smartboxchannel/EFEKTA-Open_PM_Monitor/IMAGES/001.jpg

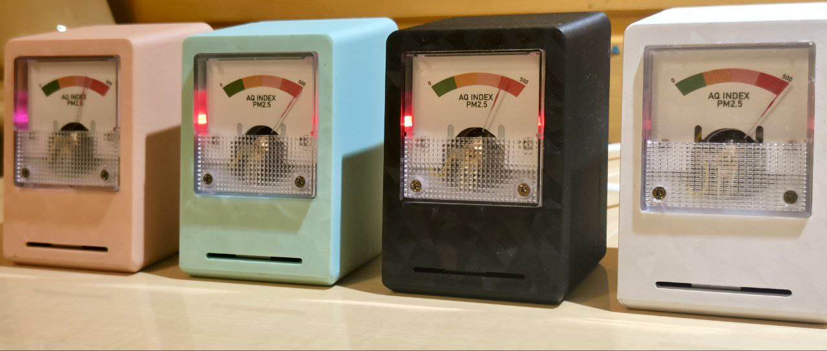
IMAGES/001.jpg
