smartboxchannel/EFEKTA-Open_PM_Monitor/IMAGES/002.jpg

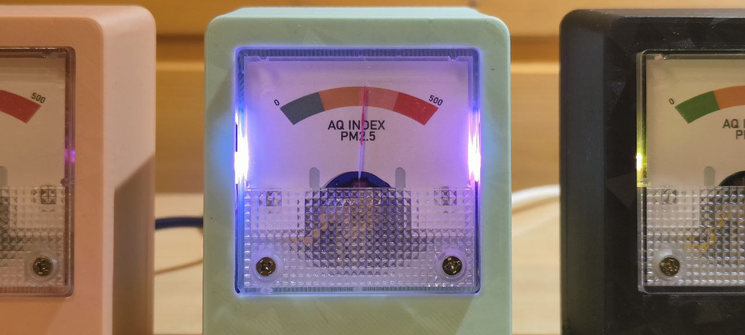
IMAGES/002.jpg
