smartboxchannel/EFEKTA-Open_PM_Monitor/IMAGES/image (5).png

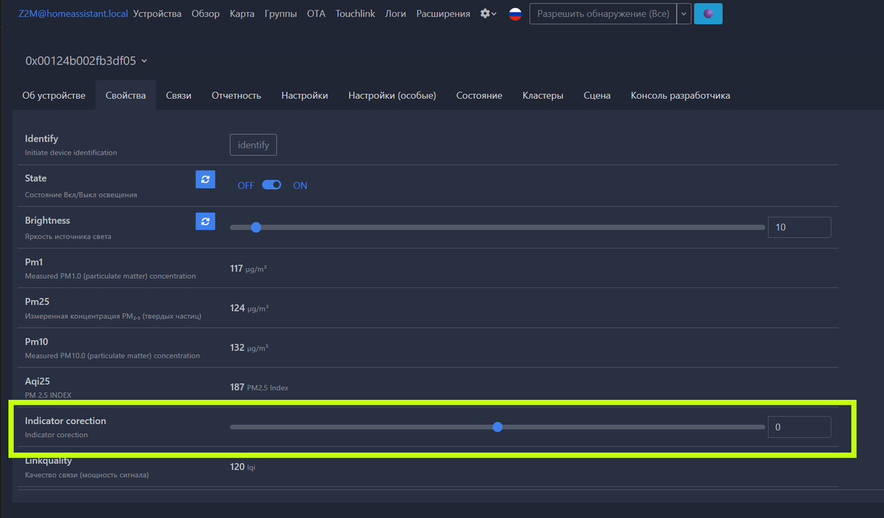
IMAGES/image (5).png
