smartboxchannel/EFEKTA-Open_PM_Monitor/PROJECT SOURCE/zstack-lib/hal_i2c.c

/**************************************************************************************************
  Filename:       hal_i2c.c
  Revised:        $Date: 2012-09-21 06:30:38 -0700 (Fri, 21 Sep 2012) $
  Revision:       $Revision: 31581 $

  Description:    This module defines the HAL I2C API for the CC2541ST. It
                  implements the I2C master.

  Copyright 2012 Texas Instruments Incorporated. All rights reserved.

  IMPORTANT: Your use of this Software is limited to those specific rights
  granted under the terms of a software license agreement between the user
  who downloaded the software, his/her employer (which must be your employer)
  and Texas Instruments Incorporated (the "License").  You may not use this
  Software unless you agree to abide by the terms of the License. The License
  limits your use, and you acknowledge, that the Software may not be modified,
  copied or distributed unless embedded on a Texas Instruments microcontroller
  or used solely and exclusively in conjunction with a Texas Instruments radio
  frequency transceiver, which is integrated into your product.  Other than for
  the foregoing purpose, you may not use, reproduce, copy, prepare derivative
  works of, modify, distribute, perform, display or sell this Software and/or
  its documentation for any purpose.

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
  Should you have any questions regarding your right to use this Software,
  contact Texas Instruments Incorporated at www.TI.com.
**************************************************************************************************/

/*********************************************************************
 * INCLUDES
 *********************************************************************/

#include "hal_i2c.h"

#include "ioCC2530.h"
#include "zcomdef.h"
#include "utils.h"

/*********************************************************************
 * MACROS
 *********************************************************************/

#define STATIC static

#if !defined HAL_I2C_RETRY_CNT
#define HAL_I2C_RETRY_CNT 3
#endif

// Default configuration uses P0.6 for SDA and P0.5 for SCL.
// Change these as needed.
#ifndef OCM_CLK_PORT
#define OCM_CLK_PORT 0
#endif

#ifndef OCM_DATA_PORT
#define OCM_DATA_PORT 0
#endif

#ifndef OCM_CLK_PIN
#define OCM_CLK_PIN 5
#endif

#ifndef OCM_DATA_PIN
#define OCM_DATA_PIN 6
#endif

#define OCM_ADDRESS (0xA0)

#define SMB_ACK         (0)
#define SMB_NAK         (1)
#define SEND_STOP       (0)
#define NOSEND_STOP     (1)
#define SEND_START      (0)
#define NOSEND_START    (1)

// OCM port I/O definitions
#define OCM_SCL BNAME(OCM_CLK_PORT, OCM_CLK_PIN)
#define OCM_SDA BNAME(OCM_DATA_PORT, OCM_DATA_PIN)

#define OCM_DATA_HIGH() { IO_DIR_PORT_PIN(OCM_DATA_PORT, OCM_DATA_PIN, IO_IN); }

#define OCM_DATA_LOW()                                                                                                                     \
    {                                                                                                                                      \
        IO_DIR_PORT_PIN(OCM_DATA_PORT, OCM_DATA_PIN, IO_OUT);                                                                              \
        OCM_SDA = 0;                                                                                                                       \
    }

/*********************************************************************
 * LOCAL VARIABLES
 *********************************************************************/

STATIC uint8 s_xmemIsInit;

/*********************************************************************
 * LOCAL FUNCTIONS PROTOTYPES
 *********************************************************************/

STATIC void hali2cSend(uint8 *buffer, uint16 len, uint8 sendStart, uint8 sendStop);
STATIC _Bool hali2cSendByte(uint8 dByte);
STATIC _Bool hali2cSendByte2(uint8 dByte);
STATIC void hali2cWrite(bool dBit);
STATIC void hali2cWrite2(bool dBit);
STATIC void hali2cClock(bool dir);
STATIC void hali2cClock2(bool dir);
STATIC void hali2cStart(void);
STATIC void hali2cStop(void);
STATIC void hali2cReceive(uint8 address, uint8 *buffer, uint16 len);
STATIC uint8 hali2cReceiveByte(void);
STATIC _Bool hali2cRead(void);
STATIC void hali2cSendDeviceAddress(uint8 address);
STATIC __near_func void hali2cWait(uint8);
static void hali2cGroudPins(void);

/*********************************************************************
 * @fn      hali2cGroudPins
 * @brief   Set I2C pins to input mode
 *********************************************************************/

static void hali2cGroudPins(void)
{
    IO_DIR_PORT_PIN(OCM_DATA_PORT, OCM_DATA_PIN, IO_IN);
    IO_DIR_PORT_PIN(OCM_CLK_PORT, OCM_CLK_PIN, IO_IN);
}

/*********************************************************************
 * @fn      HalI2CInit
 * @brief   Initializes two-wire serial I/O bus
 *********************************************************************/

void HalI2CInit(void)
{
    if (!s_xmemIsInit) {
        s_xmemIsInit = 1;

        // // Set port pins as inputs
        // IO_DIR_PORT_PIN(OCM_CLK_PORT, OCM_CLK_PIN, IO_IN);
        // IO_DIR_PORT_PIN(OCM_DATA_PORT, OCM_DATA_PIN, IO_IN);
        // //
        // // Set for general I/O operation
        // IO_FUNC_PORT_PIN(OCM_CLK_PORT, OCM_CLK_PIN, IO_GIO);
        // IO_FUNC_PORT_PIN(OCM_DATA_PORT, OCM_DATA_PIN, IO_GIO);
        // //
        // // Set I/O mode for pull-up/pull-down
        // IO_IMODE_PORT_PIN(OCM_CLK_PORT, OCM_CLK_PIN, IO_PUD);
        // IO_IMODE_PORT_PIN(OCM_DATA_PORT, OCM_DATA_PIN, IO_PUD);

        // // Set pins to pull-up
        // IO_PUD_PORT(OCM_CLK_PORT, IO_PUP);
        // IO_PUD_PORT(OCM_DATA_PORT, IO_PUP);
    }
}

/*********************************************************************
 * @fn      HalI2CReceive
 * @brief   Receives data into a buffer from an I2C slave device
 *********************************************************************/

int8 HalI2CReceive(uint8 address, uint8 *buf, uint16 len)
{
    hali2cReceive(address, buf, len);
    return 0;
}

/*********************************************************************
 * @fn      HalI2CSend
 * @brief   Sends buffer contents to an I2C slave device
 *********************************************************************/

int8 HalI2CSend(uint8 address, uint8 *buf, uint16 len)
{
    // Begin the write sequence with the address byte
    hali2cSendDeviceAddress(address);
    hali2cSend(buf, len, NOSEND_START, SEND_STOP);
    return 0;
}

/*********************************************************************
 * @fn      hali2cSend
 * @brief   Sends buffer contents to SM-Bus device
 *********************************************************************/

STATIC void hali2cSend(uint8 *buffer, uint16 len, uint8 sendStart, uint8 sendStop)
{
    uint16 i;
    uint8 retry = HAL_I2C_RETRY_CNT;

    if (!len) {
        return;
    }

    if (sendStart == SEND_START) {
        hali2cStart();
    }

    for (i = 0; i < len; i++) {
        do {
            if (hali2cSendByte(buffer[i])) // Takes care of ack polling
            {
                break;
            }
        } while (--retry);
    }

    if (sendStop == SEND_STOP) {
        hali2cStop();
    }
}

/*********************************************************************
 * @fn      hali2cSendByte
 * @brief   Serialize and send one byte to SM-Bus device
 * @return  ACK status - 0=none, 1=received
 *********************************************************************/

STATIC _Bool hali2cSendByte(uint8 dByte)
{
    uint8 i;

    for (i = 0; i < 8; i++) {
        // Send the MSB
        hali2cWrite(dByte & 0x80);
        // Next bit into MSB
        dByte <<= 1;
    }
    // Need clock low so if the SDA transitions on the next statement the
    // slave doesn't stop. Also give opportunity for slave to set SDA
    hali2cClock(0);
    OCM_DATA_HIGH(); // Set to input to receive ack...
    hali2cClock(1);
    hali2cWait(1);

    return (!OCM_SDA); // Return ACK status
}

/*********************************************************************
 * @fn      hali2cWrite
 * @brief   Send one bit to SM-Bus device
 *********************************************************************/

STATIC void hali2cWrite(bool dBit)
{
    hali2cClock(0);
    hali2cWait(1);
    if (dBit) {
        OCM_DATA_HIGH();
    } else {
        OCM_DATA_LOW();
    }

    hali2cClock(1);
    hali2cWait(1);
}

/*********************************************************************
 * @fn      hali2cClock
 * @brief   Clocks the SM-Bus. If a negative edge is going out, the
 *          I/O pin is set as an output and driven low. If a positive
 *          edge is going out, the pin is set as an input and the pin
 *          pull-up drives the line high. This way, the slave device
 *          can hold the node low if longer setup time is desired.
 *********************************************************************/

STATIC void hali2cClock(bool dir)
{
    uint8 maxWait = 10;
    if (dir) {
        IO_DIR_PORT_PIN(OCM_CLK_PORT, OCM_CLK_PIN, IO_IN);
        /* Wait until clock is high */
        while (!OCM_SCL && maxWait) {
            hali2cWait(1);
            maxWait -= 1;
        }
    } else {
        IO_DIR_PORT_PIN(OCM_CLK_PORT, OCM_CLK_PIN, IO_OUT);
        OCM_SCL = 0;
    }
    hali2cWait(1);
}

/*********************************************************************
 * @fn      hali2cClock2
 * @brief   Simplified clock function without delay
 *********************************************************************/

STATIC void hali2cClock2(bool dir)
{
    uint8 maxWait = 5;
    if (dir) {
        IO_DIR_PORT_PIN(OCM_CLK_PORT, OCM_CLK_PIN, IO_IN);
        /* Wait until clock is high */
        while (!OCM_SCL && maxWait) {
            maxWait -= 1;
        }
    } else {
        IO_DIR_PORT_PIN(OCM_CLK_PORT, OCM_CLK_PIN, IO_OUT);
        OCM_SCL = 0;
    }
}

/*********************************************************************
 * @fn      hali2cStart
 * @brief   Initiates SM-Bus communication. Makes sure that both the
 *          clock and data lines of the SM-Bus are high. Then the data
 *          line is set high and clock line is set low to start I/O.
 *********************************************************************/

STATIC void hali2cStart(void)
{
    uint8 retry = HAL_I2C_RETRY_CNT;

    // Set SCL to input but with pull-up. If slave is pulling down it will stay down.
    hali2cClock(1);

    do {
        // Wait for slave to release clock line...
        if (OCM_SCL) // Wait until the line is high...
        {
            break;
        }
        hali2cWait(1);
    } while (--retry);

    // SCL low to set SDA high so the transition will be correct.
    hali2cClock(0);
    OCM_DATA_HIGH(); // SDA high
    hali2cClock(1);  // Set up for transition
    hali2cWait(1);
    OCM_DATA_LOW(); // Start condition

    hali2cWait(1);
    hali2cClock(0);
}

/*********************************************************************
 * @fn      hali2cStop
 * @brief   Terminates SM-Bus communication. Waits until the data line
 *          is low and the clock line is high. Then sets the data line
 *          high, keeping the clock line high to stop I/O.
 *********************************************************************/

STATIC void hali2cStop(void)
{
    // Wait for clock high and data low
    hali2cClock(0);
    OCM_DATA_LOW(); // Force low with SCL low
    hali2cWait(1);

    hali2cClock(1);
    OCM_DATA_HIGH(); // Stop condition
    hali2cWait(1);

    hali2cGroudPins();
}

/*********************************************************************
 * @fn      hali2cWait
 * @brief   Busy-wait delay
 *********************************************************************/

STATIC __near_func void hali2cWait(uint8 count)
{
    while (count--) {
        asm("NOP");
    }
}

/*********************************************************************
 * @fn      hali2cReceiveByte
 * @brief   Read the 8 data bits
 *********************************************************************/

STATIC uint8 hali2cReceiveByte()
{
    int8 i, rval = 0;

    for (i = 7; i >= 0; --i) {
        if (hali2cRead()) {
            rval |= 1 << i;
        }
    }

    return rval;
}

/*********************************************************************
 * @fn      hali2cReceive
 * @brief   Reads data into a buffer
 *********************************************************************/

STATIC void hali2cReceive(uint8 address, uint8 *buffer, uint16 len)
{
    uint16 i;

    if (!len) {
        return;
    }

    hali2cSendDeviceAddress(address);

    for (i = 0; i < len - 1; i++) {
        // SCL may be high. Set SCL low. If SDA goes high when input
        // mode is set the slave won't see a STOP
        hali2cClock(0);
        OCM_DATA_HIGH();

        buffer[i] = hali2cReceiveByte();
        hali2cWrite(SMB_ACK); // Write leaves SCL high
    }

    // Condition SDA one more time...
    hali2cClock(0);
    OCM_DATA_HIGH();
    buffer[i] = hali2cReceiveByte();
    hali2cWrite(SMB_NAK);

    hali2cStop();
}

/*********************************************************************
 * @fn      hali2cRead
 * @brief   Toggle the clock line to let the slave set the data line.
 *          Then read the data line.
 * @return  TRUE if bit read is 1 else FALSE
 *********************************************************************/

STATIC _Bool hali2cRead(void)
{
    // SCL low to let slave set SDA. SCL high for SDA
    // valid and then get bit
    hali2cClock(0);
    hali2cWait(1);
    hali2cClock(1);
    hali2cWait(1);

    return OCM_SDA;
}

/*********************************************************************
 * @fn      hali2cSendDeviceAddress
 * @brief   Send only the device address with ACK polling
 *********************************************************************/

STATIC void hali2cSendDeviceAddress(uint8 address)
{
    uint8 retry = HAL_I2C_RETRY_CNT;

    do {
        hali2cStart();
        if (hali2cSendByte(address)) // Do ack polling...
        {
            break;
        }
    } while (--retry);
}

/*********************************************************************
 * @fn      I2C_ReadMultByte
 * @brief   Reads multiple bytes from an I2C device register
 *********************************************************************/

int8 I2C_ReadMultByte(uint8 address, uint8 reg, uint8 *buffer, uint16 len)
{
    uint16 i = 0;
    uint8 _address = 0;

    if (!len) {
        return I2C_ERROR;
    }

    /* Send START condition */
    hali2cStart();

    /* Set direction of transmission */
    _address = ((address << 1) | OCM_WRITE);

    /* Send Address and get acknowledgement from slave */
    if (!hali2cSendByte(_address)) {
        return I2C_ERROR;
    }

    /* Send internal register to read from */
    if (!hali2cSendByte(reg)) {
        return I2C_ERROR;
    }

    /* Send RESTART condition */
    hali2cStart();

    /* Set direction of transmission */
    _address = ((address << 1) | OCM_READ);
    /* Send Address and get acknowledgement from slave */
    if (!hali2cSendByte(_address)) {
        return I2C_ERROR;
    }

    while (len) {
        // SCL may be high. Set SCL low. If SDA goes high when input
        // mode is set the slave won't see a STOP
        hali2cClock(0);
        OCM_DATA_HIGH();
        buffer[i] = hali2cReceiveByte();
        // Acknowledgement if not sending last byte
        if (len > 1) {
            hali2cWrite(SMB_ACK); // Write leaves SCL high
        }

        // Increment buffer register
        i++;
        // Decrement the read bytes counter
        len--;
    }

    // Condition SDA one more time...
    hali2cClock(0);
    OCM_DATA_HIGH();
    hali2cWrite(SMB_NAK);

    hali2cStop();

    return I2C_SUCCESS;
}

/*********************************************************************
 * @fn      I2C_WriteMultByte
 * @brief   Writes multiple bytes to an I2C device register
 *********************************************************************/

int8 I2C_WriteMultByte(uint8 address, uint8 reg, uint8 *buffer, uint16 len)
{
    uint16 i = 0;
    uint8 _address = 0;

    if (!len) {
        return I2C_ERROR;
    }

    /* Send START condition */
    hali2cStart();

    /* Set direction of transmission */
    _address = ((address << 1) | OCM_WRITE);

    /* Send Address and get acknowledgement from slave */
    if (!hali2cSendByte(_address)) {
        return I2C_ERROR;
    }

    /* Send internal register to write to */
    if (!hali2cSendByte(reg)) {
        return I2C_ERROR;
    }

    /* Write data into register */
    while (len) {
        /* Send data byte and get acknowledgement from slave */
        if (!hali2cSendByte2(buffer[i])) {
            return I2C_ERROR;
        }

        // Increment buffer register
        i++;
        // Decrement the write bytes counter
        len--;
    }

    hali2cStop();
    return I2C_SUCCESS;
}

/*********************************************************************
 * @fn      hali2cSendByte2
 * @brief   Serialize and send one byte (optimized version)
 *********************************************************************/

STATIC _Bool hali2cSendByte2(uint8 dByte)
{
    uint8 i;

    for (i = 0; i < 8; i++) {
        // Send the MSB
        hali2cWrite2(dByte & 0x80);
        // Next bit into MSB
        dByte <<= 1;
    }
    // Need clock low so if the SDA transitions on the next statement the
    // slave doesn't stop. Also give opportunity for slave to set SDA
    hali2cClock2(0);
    OCM_DATA_HIGH(); // Set to input to receive ack...
    hali2cClock2(1);

    return (!OCM_SDA); // Return ACK status
}

/*********************************************************************
 * @fn      hali2cWrite2
 * @brief   Send one bit (optimized version)
 *********************************************************************/

STATIC void hali2cWrite2(bool dBit)
{
    hali2cClock2(0);
    if (dBit) {
        OCM_DATA_HIGH();
    } else {
        OCM_DATA_LOW();
    }
    hali2cClock2(1);
}
