smartboxchannel/EFEKTA-Open_PM_Monitor/PROJECT SOURCE/Source/zcl_ota.h

/******************************************************************************
 * Filename:       zcl_ota.h
 * Description:    ZCL Over-the-Air Upgrade Cluster definitions
 *
 * Copyright 2010-2014 Texas Instruments Incorporated. All rights reserved.
 *****************************************************************************/

#ifndef ZCL_OTA_H
#define ZCL_OTA_H

#ifdef __cplusplus
extern "C"
{
#endif

/******************************************************************************
 * INCLUDES
 *****************************************************************************/

#include "zcl.h"
#include "ota_common.h"

/******************************************************************************
 * CONSTANTS - Profile and Device IDs
 *****************************************************************************/

#define ZCL_SE_PROFILE_ID                             0x0109
#define ZCL_HA_PROFILE_ID                             0x0104

#define ZCL_SE_DEVICEID_PHYSICAL                      0x0507

/******************************************************************************
 * CONSTANTS - OTA Protocol Limits
 *****************************************************************************/

#define OTA_MIN_FILENAME_LEN                          27
#define OTA_MAX_MTU                                   32
#define OTA_MAX_BLOCK_RETRIES                         10
#define OTA_MAX_END_REQ_RETRIES                       2
#define OTA_MAX_BLOCK_RSP_WAIT_TIME                   ((uint16)5000)

/******************************************************************************
 * CONSTANTS - Simple Descriptor Values
 *****************************************************************************/

#define ZCL_OTA_ENDPOINT                              14

#ifdef OTA_HA
#define ZCL_OTA_SAMPLE_PROFILE_ID                     ZCL_HA_PROFILE_ID
#define ZCL_OTA_SAMPLE_DEVICEID                       0x000C
#else
#define ZCL_OTA_SAMPLE_PROFILE_ID                     ZCL_SE_PROFILE_ID
#define ZCL_OTA_SAMPLE_DEVICEID                       ZCL_SE_DEVICEID_PHYSICAL
#endif

#define ZCL_OTA_DEVICE_VERSION                        0
#define ZCL_OTA_FLAGS                                 0

/******************************************************************************
 * CONSTANTS - OTA Device Identification
 *****************************************************************************/

#if !defined OTA_MANUFACTURER_ID
#define OTA_MANUFACTURER_ID                           0x5678
#endif

#if !defined OTA_TYPE_ID
#define OTA_TYPE_ID                                   0x1234
#endif

/******************************************************************************
 * CONSTANTS - OTA Header Definitions
 *****************************************************************************/

#define OTA_HDR_VERSION                               0x0100

/* OTA Header Field Control Bits */
#define OTA_HDR_FC_SEC_CRED_PRESENT                   0x01
#define OTA_HDR_FC_DEV_SPEC_FILE                      0x02
#define OTA_HDR_FC_HW_VER_PRESENT                     0x04

#define OTA_HDR_MFG_MATCH_ALL                         0xFFFF
#define OTA_HDR_FILE_VER_MATCH_ALL                    0xFFFFFFFF

/* OTA Header Image Types */
#define OTA_HDR_IMAGE_SEC_CRED                        0xFFC0
#define OTA_HDR_IMAGE_CONFIG                          0xFFC1
#define OTA_HDR_IMAGE_LOG                             0xFFC2
#define OTA_HDR_IMAGE_MATCH_ALL                       0xFFFF

/* OTA ZigBee Stack Versions */
#define OTA_STACK_VER_2006                            0x0000
#define OTA_STACK_VER_2007                            0x0001
#define OTA_STACK_VER_PRO                             0x0002
#define OTA_STACK_VER_IP                              0x0003

/* OTA Security Credential Versions */
#define OTA_SEC_CRED_VER_10                           0x00
#define OTA_SEC_CRED_VER_1X                           0x01
#define OTA_SEC_CRED_VER_20                           0x02

/******************************************************************************
 * CONSTANTS - OTA Attribute IDs
 *****************************************************************************/

#define ATTRID_UPGRADE_SERVER_ID                      0x0000
#define ATTRID_FILE_OFFSET                            0x0001
#define ATTRID_CURRENT_FILE_VERSION                   0x0002
#define ATTRID_CURRENT_ZIGBEE_STACK_VERSION           0x0003
#define ATTRID_DOWNLOADED_FILE_VERSION                0x0004
#define ATTRID_DOWNLOADED_ZIGBEE_STACK_VERSION        0x0005
#define ATTRID_IMAGE_UPGRADE_STATUS                   0x0006
#define ATTRID_MANUFACTURER_ID                        0x0007
#define ATTRID_IMAGE_TYPE_ID                          0x0008
#define ATTRID_MINIMUM_BLOCK_REQ_DELAY                0x0009
#define ATTRID_IMAGE_STAMP                            0x000A

/******************************************************************************
 * CONSTANTS - OTA Upgrade Status
 *****************************************************************************/

#define OTA_STATUS_NORMAL                             0x00
#define OTA_STATUS_IN_PROGRESS                        0x01
#define OTA_STATUS_COMPLETE                           0x02
#define OTA_STATUS_UPGRADE_WAIT                       0x03
#define OTA_STATUS_COUNTDOWN                          0x04
#define OTA_STATUS_WAIT_FOR_MORE                      0x05

#define OTA_UPGRADE_TIME_WAIT                         0xFFFFFFFF
#define OTA_UPGRADE_DELAY                             60

/******************************************************************************
 * CONSTANTS - OTA Cluster Command IDs
 *****************************************************************************/

#define COMMAND_IMAGE_NOTIFY                          0x00
#define COMMAND_QUERY_NEXT_IMAGE_REQ                  0x01
#define COMMAND_QUERY_NEXT_IMAGE_RSP                  0x02
#define COMMAND_IMAGE_BLOCK_REQ                       0x03
#define COMMAND_IMAGE_PAGE_REQ                        0x04
#define COMMAND_IMAGE_BLOCK_RSP                       0x05
#define COMMAND_UPGRADE_END_REQ                       0x06
#define COMMAND_UPGRADE_END_RSP                       0x07
#define COMMAND_QUERY_SPECIFIC_FILE_REQ               0x08
#define COMMAND_QUERY_SPECIFIC_FILE_RSP               0x09

/******************************************************************************
 * CONSTANTS - Command Payload Lengths
 *****************************************************************************/

#define PAYLOAD_MAX_LEN_IMAGE_NOTIFY                  10
#define PAYLOAD_MAX_LEN_QUERY_NEXT_IMAGE_REQ          11
#define PAYLOAD_MAX_LEN_QUERY_NEXT_IMAGE_RSP          13
#define PAYLOAD_MAX_LEN_IMAGE_BLOCK_REQ               24
#define PAYLOAD_MAX_LEN_IMAGE_PAGE_REQ                26
#define PAYLOAD_MAX_LEN_IMAGE_BLOCK_RSP               14
#define PAYLOAD_MAX_LEN_UPGRADE_END_REQ               9
#define PAYLOAD_MAX_LEN_UPGRADE_END_RSP               16
#define PAYLOAD_MAX_LEN_QUERY_SPECIFIC_FILE_REQ       18
#define PAYLOAD_MAX_LEN_QUERY_SPECIFIC_FILE_RSP       13

#define PAYLOAD_MIN_LEN_IMAGE_NOTIFY                  2
#define PAYLOAD_MIN_LEN_QUERY_NEXT_IMAGE_REQ          9
#define PAYLOAD_MIN_LEN_QUERY_NEXT_IMAGE_RSP          1
#define PAYLOAD_MIN_LEN_IMAGE_BLOCK_REQ               14
#define PAYLOAD_MIN_LEN_IMAGE_PAGE_REQ                18
#define PAYLOAD_MIN_LEN_IMAGE_BLOCK_RSP               14
#define PAYLOAD_MIN_LEN_IMAGE_BLOCK_WAIT              11
#define PAYLOAD_MIN_LEN_UPGRADE_END_REQ               1
#define PAYLOAD_MIN_LEN_UPGRADE_END_RSP               16
#define PAYLOAD_MIN_LEN_QUERY_SPECIFIC_FILE_REQ       18
#define PAYLOAD_MIN_LEN_QUERY_SPECIFIC_FILE_RSP       1

/******************************************************************************
 * CONSTANTS - Image Block Request Field Control
 *****************************************************************************/

#define OTA_BLOCK_FC_GENERIC                          0x00
#define OTA_BLOCK_FC_NODES_IEEE_PRESENT               0x01
#define OTA_BLOCK_FC_REQ_DELAY_PRESENT                0x02

/******************************************************************************
 * CONSTANTS - Image Notify Payload Types
 *****************************************************************************/

#define NOTIFY_PAYLOAD_JITTER                         0x00
#define NOTIFY_PAYLOAD_JITTER_MFG                     0x01
#define NOTIFY_PAYLOAD_JITTER_MFG_TYPE                0x02
#define NOTIFY_PAYLOAD_JITTER_MFG_TYPE_VERS           0x03

/******************************************************************************
 * CONSTANTS - Client Task Events
 *****************************************************************************/

#define ZCL_OTA_IMAGE_BLOCK_WAIT_EVT                  0x0001
#define ZCL_OTA_UPGRADE_WAIT_EVT                      0x0002
#define ZCL_OTA_QUERY_SERVER_EVT                      0x0004
#define ZCL_OTA_BLOCK_RSP_TO_EVT                      0x0008
#define ZCL_OTA_IMAGE_QUERY_TO_EVT                    0x0010
#define ZCL_OTA_IMAGE_BLOCK_REQ_DELAY_EVT             0x0020
#define ZCL_OTA_SEND_MATCH_DESCRIPTOR_EVT             0x0040
#define ZCL_OTA_SEND_IEEE_ADD_REQ_EVT                 0x0080

/******************************************************************************
 * CONSTANTS - OTA Element Tag Identifiers
 *****************************************************************************/

#define OTA_UPGRADE_IMAGE_TAG_ID                      0
#define OTA_ECDSA_SIGNATURE_TAG_ID                    1
#define OTA_ECDSA_CERT_TAG_ID                         2

/******************************************************************************
 * CONSTANTS - OTA Client Processing States
 *****************************************************************************/

#define ZCL_OTA_PD_MAGIC_0_STATE                      0
#define ZCL_OTA_PD_MAGIC_1_STATE                      1
#define ZCL_OTA_PD_MAGIC_2_STATE                      2
#define ZCL_OTA_PD_MAGIC_3_STATE                      3
#define ZCL_OTA_PD_HDR_LEN1_STATE                     4
#define ZCL_OTA_PD_HDR_LEN2_STATE                     5
#define ZCL_OTA_PD_STK_VER1_STATE                     6
#define ZCL_OTA_PD_STK_VER2_STATE                     7
#define ZCL_OTA_PD_CONT_HDR_STATE                     8
#define ZCL_OTA_PD_ELEM_TAG1_STATE                    9
#define ZCL_OTA_PD_ELEM_TAG2_STATE                    10
#define ZCL_OTA_PD_ELEM_LEN1_STATE                    11
#define ZCL_OTA_PD_ELEM_LEN2_STATE                    12
#define ZCL_OTA_PD_ELEM_LEN3_STATE                    13
#define ZCL_OTA_PD_ELEM_LEN4_STATE                    14
#define ZCL_OTA_PD_ELEMENT_STATE                      15

/******************************************************************************
 * CONSTANTS - Callback Events
 *****************************************************************************/

#define ZCL_OTA_START_CALLBACK                        0
#define ZCL_OTA_DL_COMPLETE_CALLBACK                  1

#define OTA_SEND_BLOCK_WAIT                           0

/******************************************************************************
 * TYPEDEFS - Command Parameter Structures
 *****************************************************************************/

typedef struct
{
    uint8 payloadType;
    uint8 queryJitter;
    zclOTA_FileID_t fileId;
} zclOTA_ImageNotifyParams_t;

typedef struct
{
    uint8 fieldControl;
    zclOTA_FileID_t fileId;
    uint16 hardwareVersion;
} zclOTA_QueryNextImageReqParams_t;

typedef struct
{
    uint8 status;
    zclOTA_FileID_t fileId;
    uint32 imageSize;
} zclOTA_QueryImageRspParams_t;

typedef struct
{
    uint8 fieldControl;
    zclOTA_FileID_t fileId;
    uint32 fileOffset;
    uint8 maxDataSize;
    uint8 nodeAddr[Z_EXTADDR_LEN];
    uint16 blockReqDelay;
} zclOTA_ImageBlockReqParams_t;

typedef struct
{
    uint8 fieldControl;
    zclOTA_FileID_t fileId;
    uint32 fileOffset;
    uint8 maxDataSize;
    uint16 pageSize;
    uint16 responseSpacing;
    uint8 nodeAddr[Z_EXTADDR_LEN];
} zclOTA_ImagePageReqParams_t;

typedef struct
{
    zclOTA_FileID_t fileId;
    uint32 fileOffset;
    uint8 dataSize;
    uint8 *pData;
} imageBlockRspSuccess_t;

typedef struct
{
    uint32 currentTime;
    uint32 requestTime;
    uint16 blockReqDelay;
} imageBlockRspWait_t;

typedef union
{
    imageBlockRspSuccess_t success;
    imageBlockRspWait_t wait;
} imageBlockRsp_t;

typedef struct
{
    uint8 status;
    imageBlockRsp_t rsp;
} zclOTA_ImageBlockRspParams_t;

typedef struct
{
    uint8 status;
    zclOTA_FileID_t fileId;
} zclOTA_UpgradeEndReqParams_t;

typedef struct
{
    zclOTA_FileID_t fileId;
    uint32 currentTime;
    uint32 upgradeTime;
} zclOTA_UpgradeEndRspParams_t;

typedef struct
{
    uint8 nodeAddr[Z_EXTADDR_LEN];
    zclOTA_FileID_t fileId;
    uint16 stackVersion;
} zclOTA_QuerySpecificFileReqParams_t;

typedef union
{
    zclOTA_QueryImageRspParams_t  queryNextImageRsp;
    zclOTA_ImageBlockRspParams_t  imageBlockRsp;
    zclOTA_UpgradeEndRspParams_t  upgradeEndRsp;
    zclOTA_QueryImageRspParams_t  querySpecificFileRsp;
} zclOTA_RspParams_t;

typedef struct
{
    osal_event_hdr_t hdr;
    uint8 ota_event;
} zclOTA_CallbackMsg_t;

/******************************************************************************
 * GLOBAL VARIABLES
 *****************************************************************************/

extern uint8 zclOTA_UpgradeServerID[Z_EXTADDR_LEN];
extern uint32 zclOTA_FileOffset;
extern uint32 zclOTA_CurrentFileVersion;
extern uint16 zclOTA_CurrentZigBeeStackVersion;
extern uint32 zclOTA_DownloadedFileVersion;
extern uint16 zclOTA_DownloadedZigBeeStackVersion;
extern uint8 zclOTA_ImageUpgradeStatus;
extern uint16 zclOTA_ManufacturerId;
extern uint16 zclOTA_ImageType;
extern uint16 zclOTA_MinBlockReqDelay;

/******************************************************************************
 * FUNCTION PROTOTYPES
 *****************************************************************************/

/*
 * Register an application to receive OTA callback messages
 */
extern void zclOTA_Register(uint8 applicationTaskId);

/*
 * Request next image update from OTA server after discovery
 */
extern void zclOTA_RequestNextUpdate(uint16 srvAddr, uint8 srvEndPoint);

/*
 * Enable or disable OTA operation
 */
extern void zclOTA_PermitOta(uint8 permit);

/*
 * Initialize OTA Client Task
 */
extern void zclOTA_Init(uint8 task_id);

/*
 * OTA Task event loop processor
 */
extern uint16 zclOTA_event_loop(uint8 task_id, uint16 events);

/*
 * Get current ZCL OTA status
 */
extern uint8 zclOTA_getStatus(void);

#if defined(OTA_SERVER) && (OTA_SERVER == TRUE)
/*
 * Send Image Notify to OTA client (Server function)
 */
extern ZStatus_t zclOTA_SendImageNotify(afAddrType_t *dstAddr,
                                         zclOTA_ImageNotifyParams_t *pParams);
#endif

#ifdef __cplusplus
}
#endif

#endif /* ZCL_OTA_H */
