smartboxchannel/EFEKTA-Open_PM_Monitor/PROJECT SOURCE/zstack-lib/factory_reset.h

#ifndef FACTORY_RESET_H
#define FACTORY_RESET_H

/******************************************************************************
 * Constants - Event IDs
 *****************************************************************************/

#define FACTORY_RESET_EVT               0x1000
#define FACTORY_BOOTCOUNTER_RESET_EVT   0x2000
#define FACTORY_LED_EVT                 0x4000
#define FACTORY_LEDOFF_EVT              0x8000

/******************************************************************************
 * Constants - Factory Reset Configuration
 *****************************************************************************/

#ifndef FACTORY_RESET_HOLD_TIME_LONG
    #define FACTORY_RESET_HOLD_TIME_LONG ((uint32)9 * 1000)   // 9 seconds
#endif

#ifndef FACTORY_RESET_HOLD_TIME_FAST
    #define FACTORY_RESET_HOLD_TIME_FAST 2000                 // 2 seconds
#endif

#ifndef FACTORY_RESET_BOOTCOUNTER_MAX_VALUE
    #define FACTORY_RESET_BOOTCOUNTER_MAX_VALUE 5
#endif

#ifndef FACTORY_RESET_BOOTCOUNTER_RESET_TIME
    #define FACTORY_RESET_BOOTCOUNTER_RESET_TIME 10 * 1000    // 10 seconds
#endif

#ifndef FACTORY_RESET_BY_LONG_PRESS
    #define FACTORY_RESET_BY_LONG_PRESS TRUE
#endif

#ifndef FACTORY_RESET_BY_LONG_PRESS_PORT
    #define FACTORY_RESET_BY_LONG_PRESS_PORT 0x00
#endif

#ifndef FACTORY_RESET_BY_BOOT_COUNTER
    #define FACTORY_RESET_BY_BOOT_COUNTER TRUE
#endif

/******************************************************************************
 * Function Prototypes
 *****************************************************************************/

extern void zclFactoryResetter_Init(uint8 task_id);
extern uint16 zclFactoryResetter_loop(uint8 task_id, uint16 events);
extern void zclFactoryResetter_HandleKeys(uint8 portAndAction, uint8 keyCode);

#endif /* FACTORY_RESET_H */
